kholia/Easy-Digital-Beacons-v1/CW-Beacon-Without-Si5351/Raspberry-Pi-Pico-Pinout.jpg

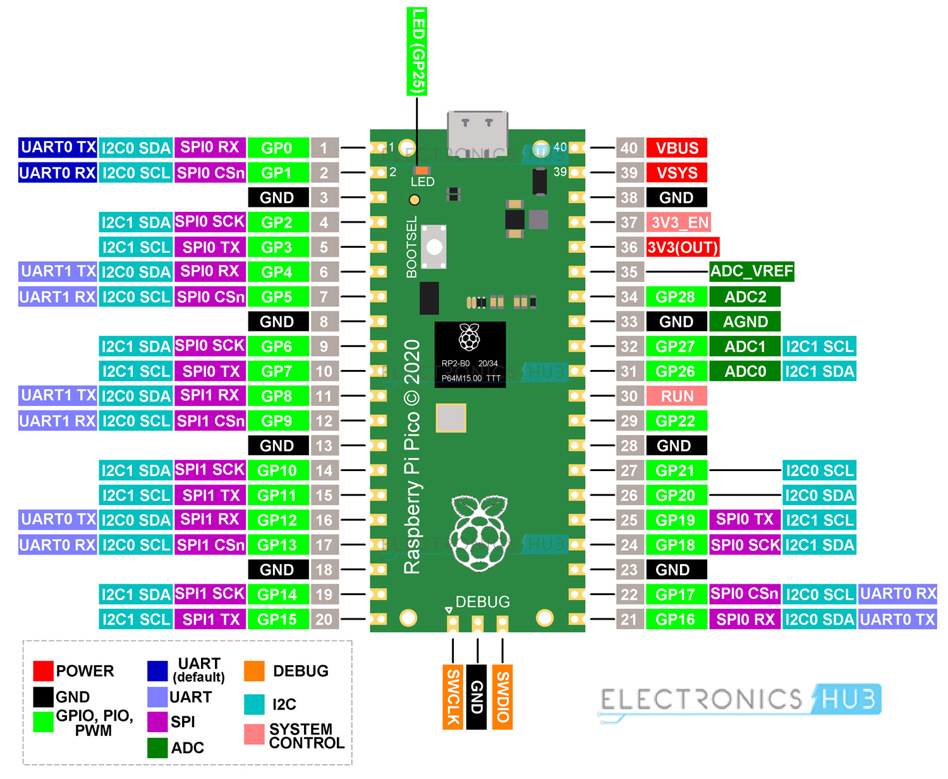
CW-Beacon-Without-Si5351/Raspberry-Pi-Pico-Pinout.jpg
