kholia/Easy-Digital-Beacons-v1/F4GOH-PCB-FST4W-LCD/balise-hf.png

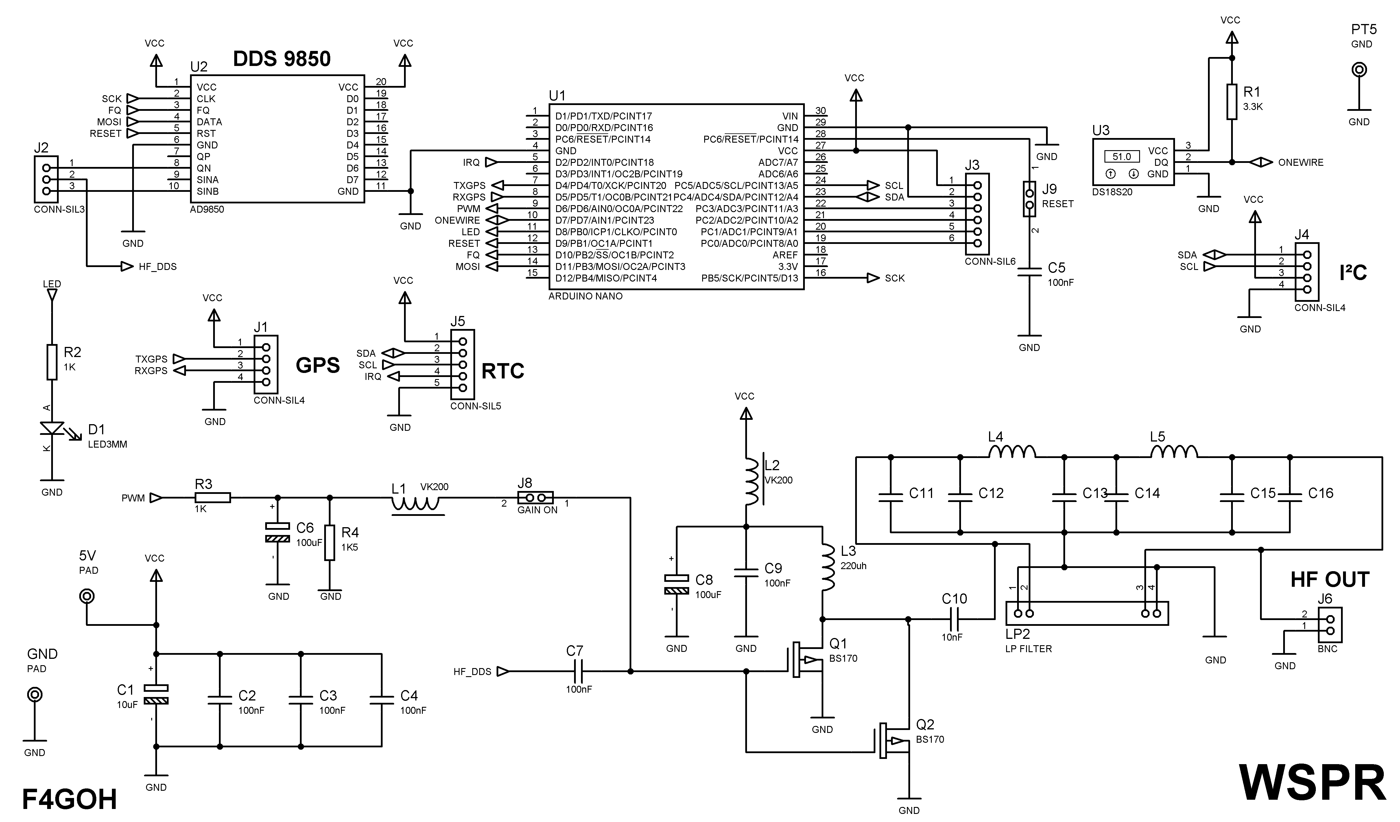
F4GOH-PCB-FST4W-LCD/balise-hf.png
