kholia/Easy-Digital-Beacons-v1/FST4W-GPS-v3-Arduino/Arduino-Nano-Pin-Description-952x1024.jpg

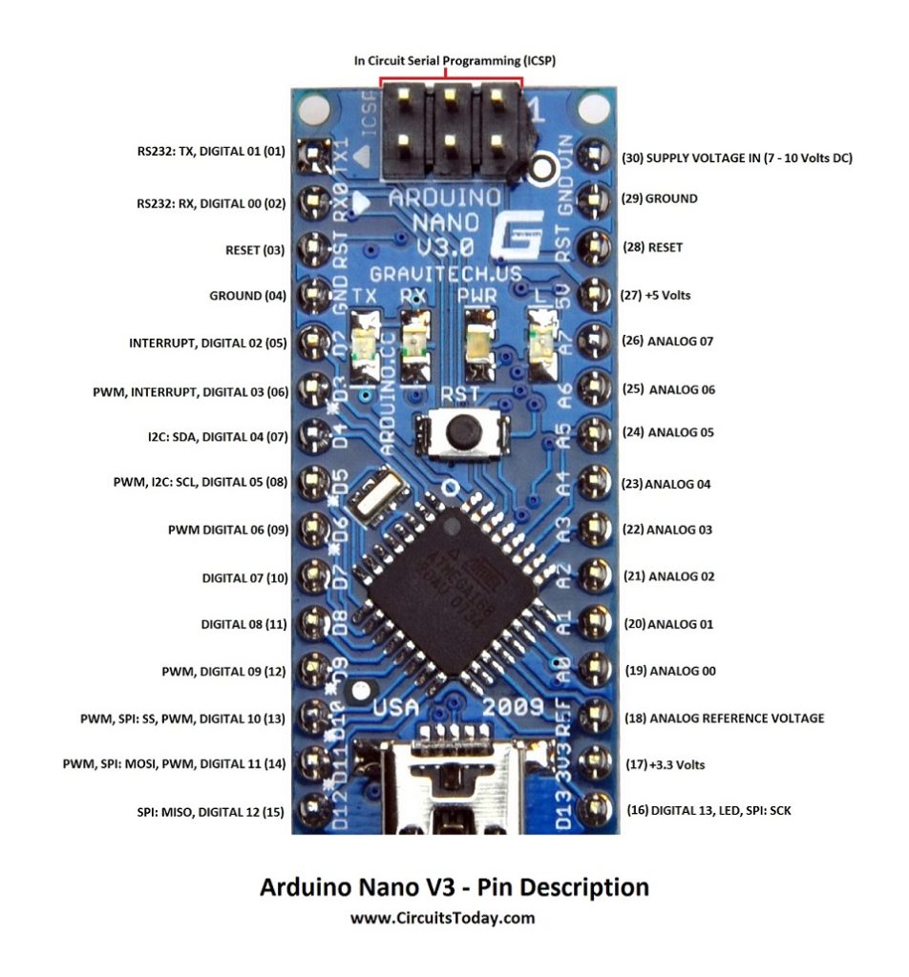
FST4W-GPS-v3-Arduino/Arduino-Nano-Pin-Description-952x1024.jpg
