kholia/Easy-Digital-Beacons-v1/images/MPPico-Base-06-800x800.png

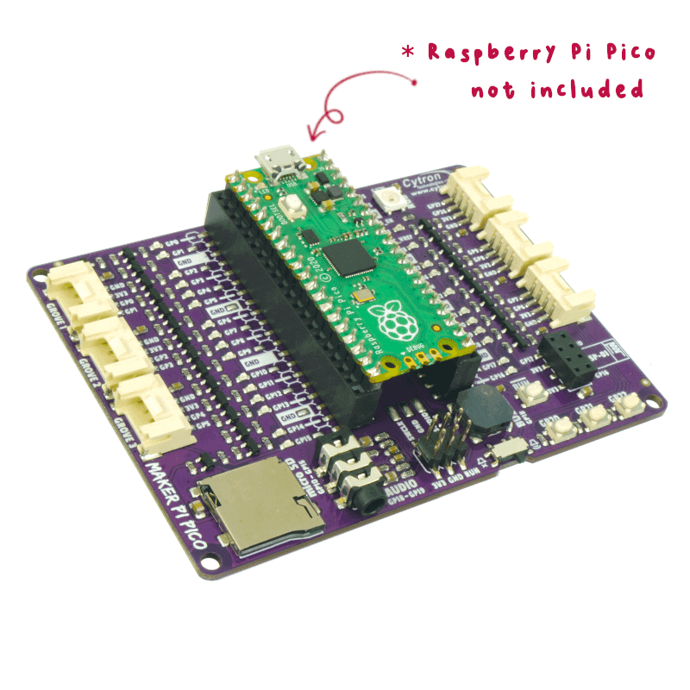
images/MPPico-Base-06-800x800.png
