kholia/Easy-Digital-Beacons-v1/images/Screenshot_2021-10-10_12-11-27.png

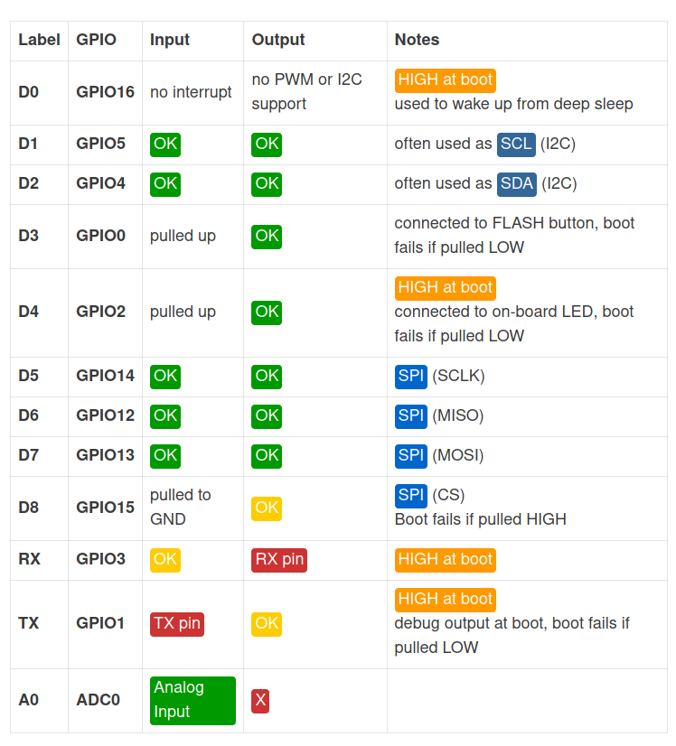
images/Screenshot_2021-10-10_12-11-27.png
