kholia/Easy-Digital-Beacons-v1/Pico-FT8-Beacon-OnlyGPS/Schematic-From-Tony.jpeg

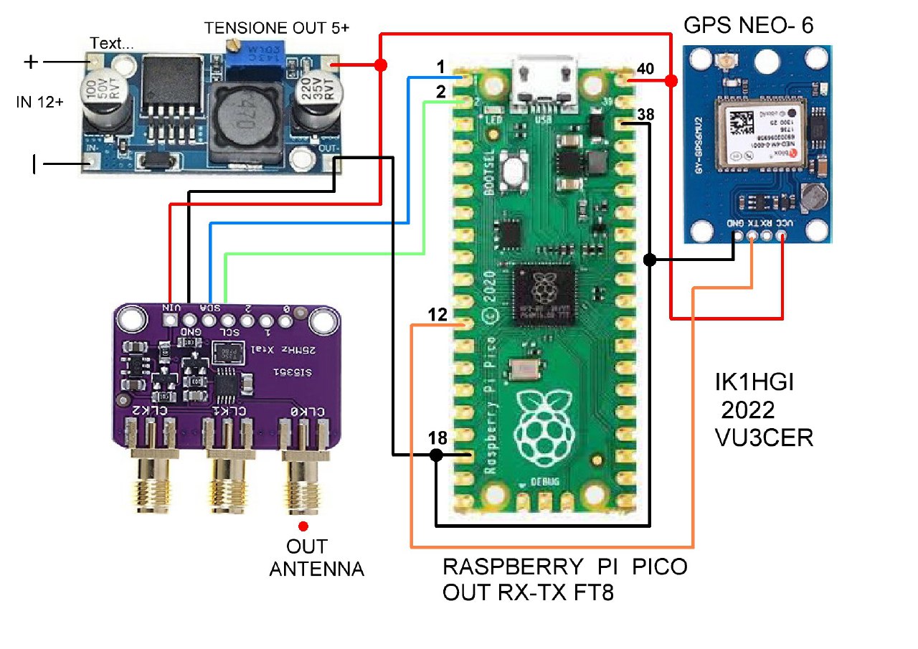
Pico-FT8-Beacon-OnlyGPS/Schematic-From-Tony.jpeg
