kholia/Easy-Digital-Beacons-v1/Pixie-WSPR-ESP8266/pixie+modified.jpg

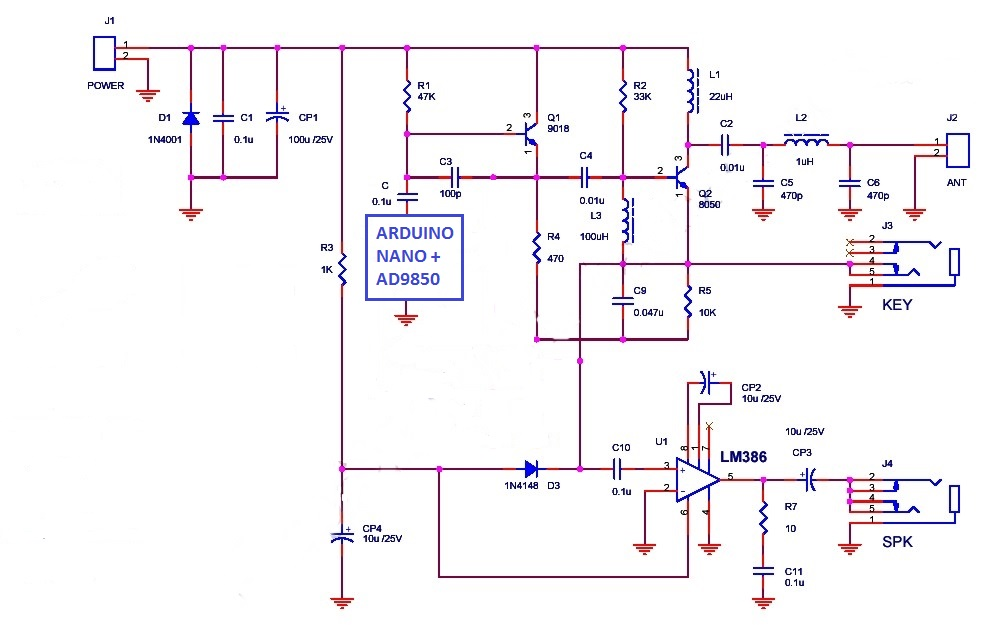
Pixie-WSPR-ESP8266/pixie+modified.jpg
