kholia/Easy-Digital-Beacons-v1/Pixie-WSPR-ESP8266/pixie+schematic.jpg

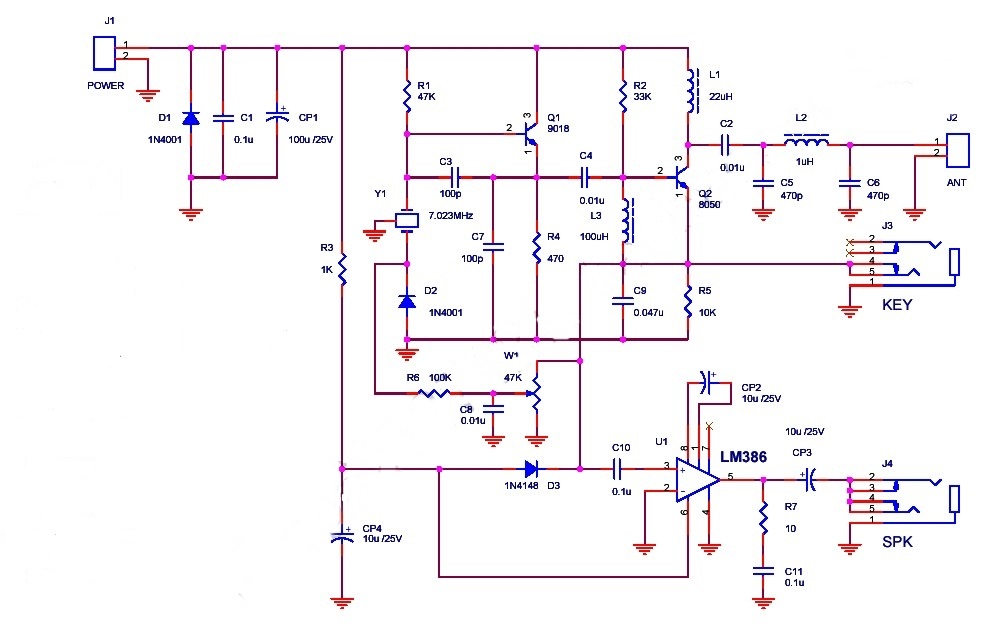
Pixie-WSPR-ESP8266/pixie+schematic.jpg
