kholia/Easy-Digital-Beacons-v1/Pixie-WSPR-ESP8266/Pixie-WSPR-Hack.jpg

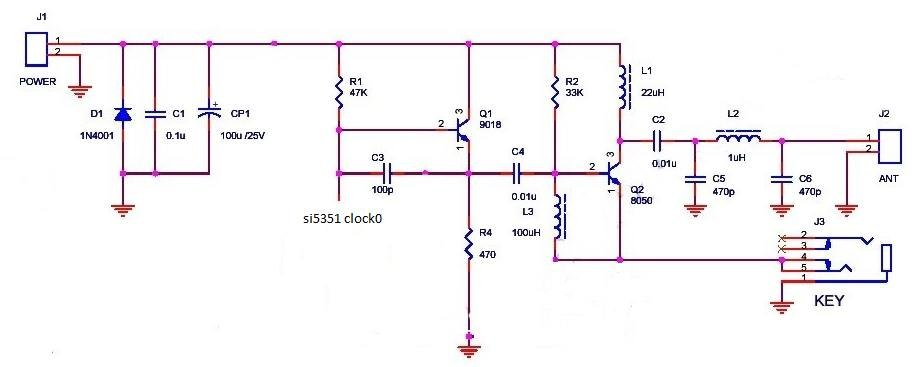
Pixie-WSPR-ESP8266/Pixie-WSPR-Hack.jpg
