kholia/Easy-Digital-Beacons-v1/Pixie-WSPR-ESP8266/Real-Life-Picture-2.jpg

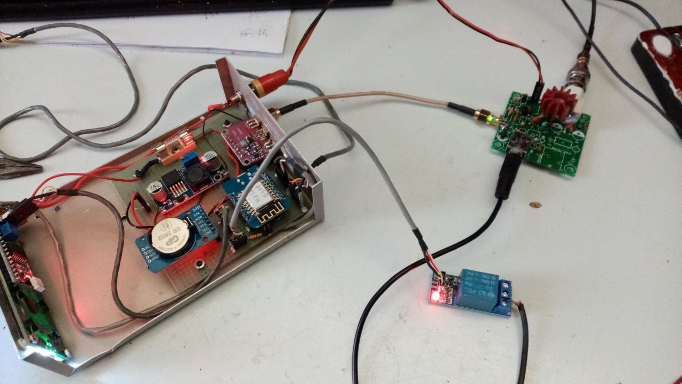
Pixie-WSPR-ESP8266/Real-Life-Picture-2.jpg
