kholia/Easy-Digital-Beacons-v1/Pixie-WSPR-ESP8266/Real-Life-Picture.jpg

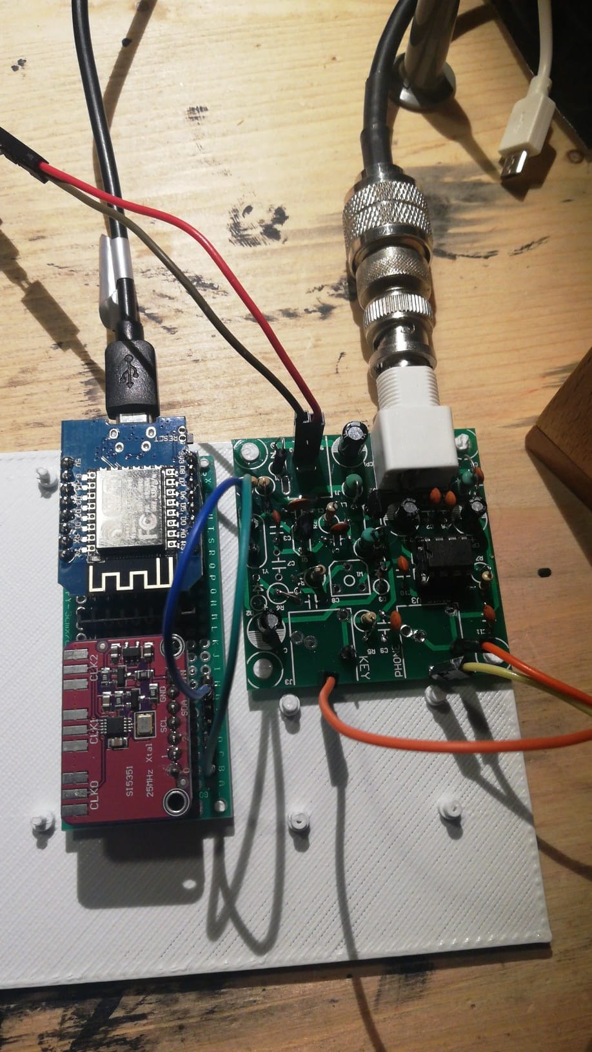
Pixie-WSPR-ESP8266/Real-Life-Picture.jpg
