kholia/Easy-Digital-Beacons-v1/screenshots/1 Channel Relay Module (Active Low Control).jpg

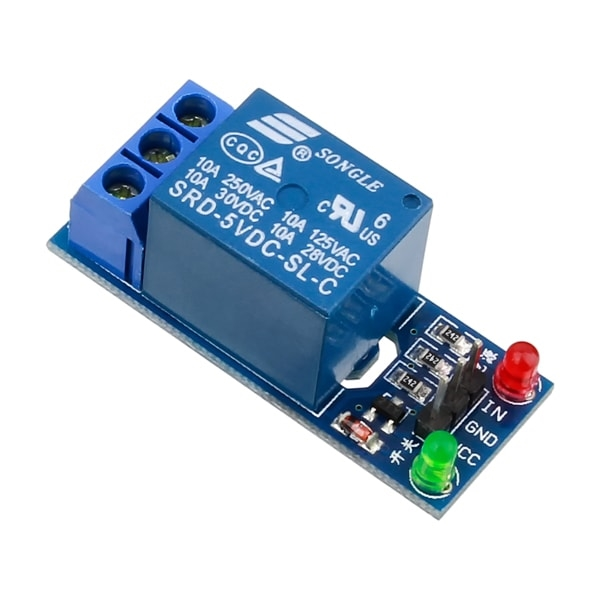
screenshots/1 Channel Relay Module (Active Low Control).jpg
