kholia/Easy-Digital-Beacons-v1/screenshots/120TR-Screenshot_2022-03-21_17-04-42.png

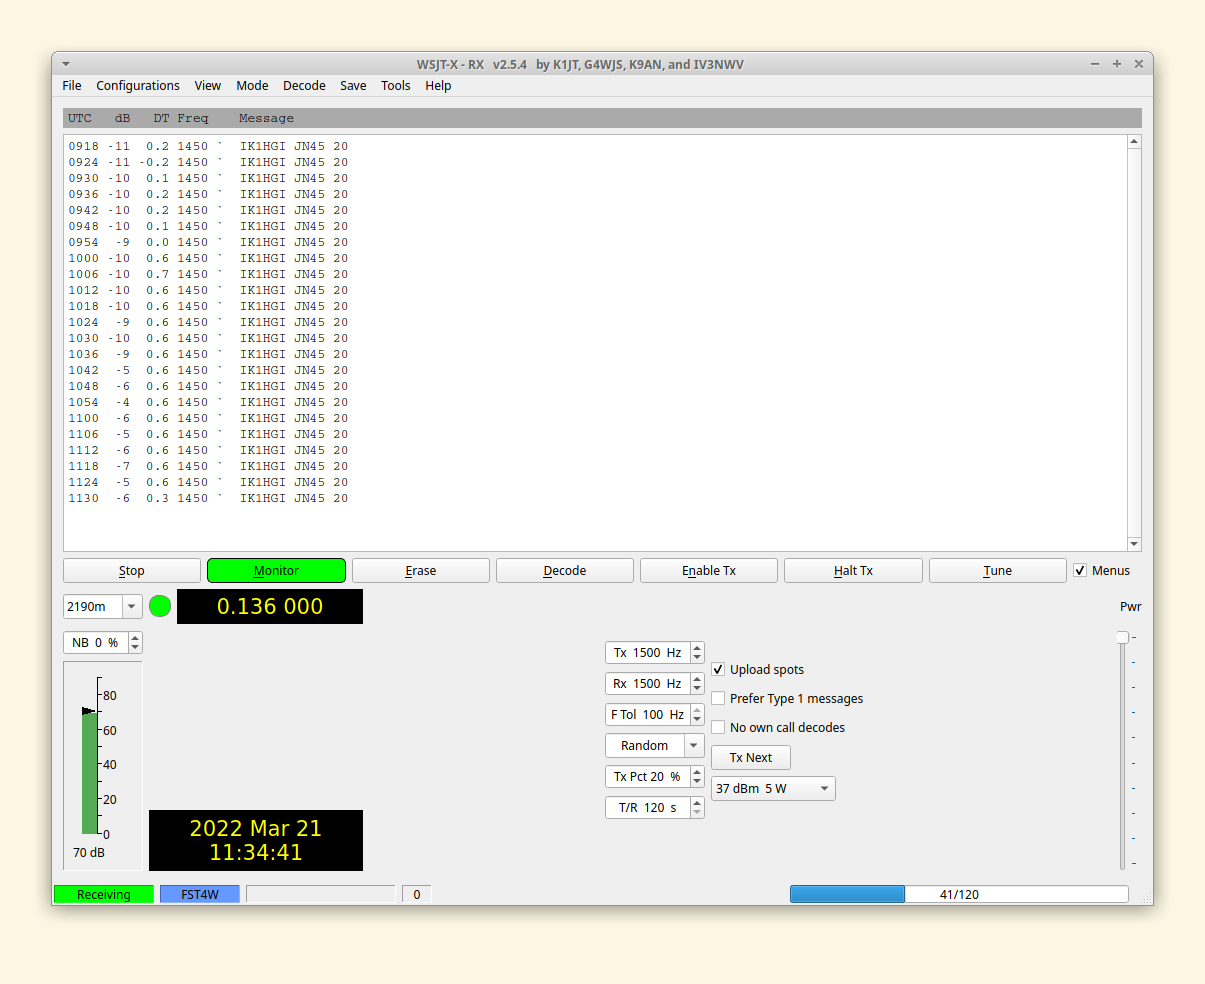
screenshots/120TR-Screenshot_2022-03-21_17-04-42.png
