kholia/Easy-Digital-Beacons-v1/screenshots/300TR-Multiple-Success-Screenshot_2022-03-21_18-41-07.png

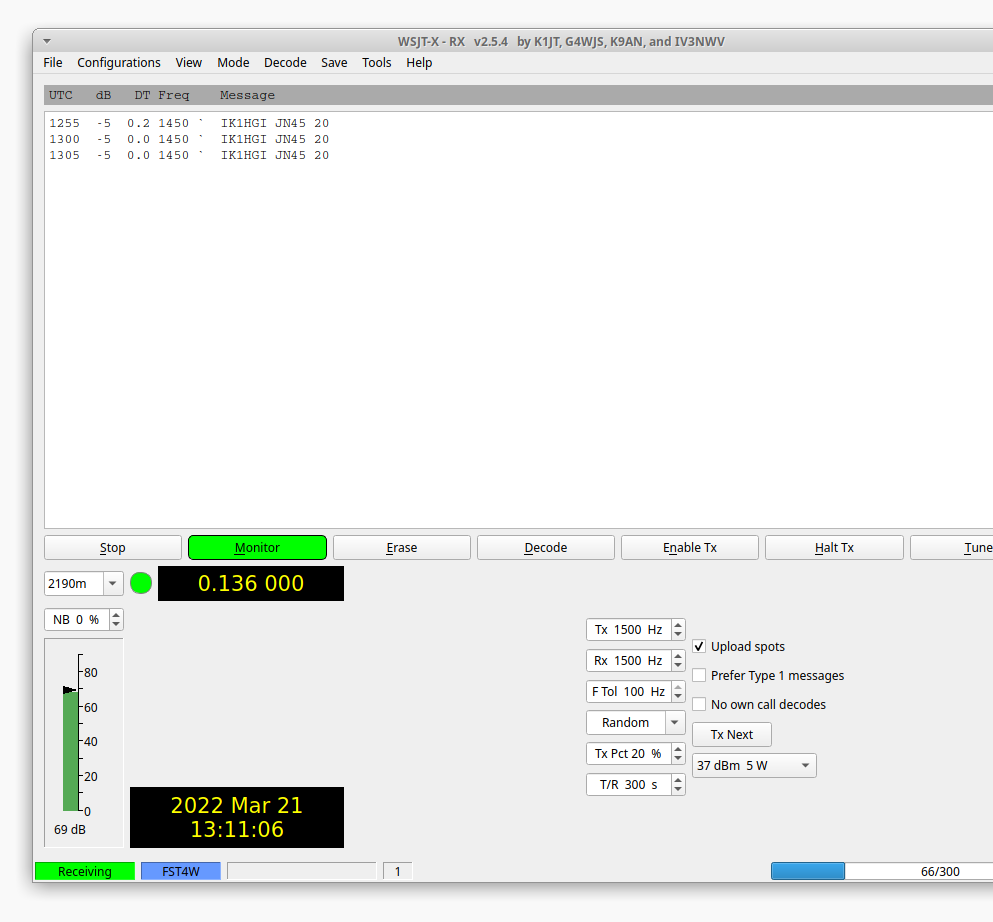
screenshots/300TR-Multiple-Success-Screenshot_2022-03-21_18-41-07.png
