kholia/Easy-Digital-Beacons-v1/screenshots/300TR-Screenshot_2022-03-21_18-15-22.png

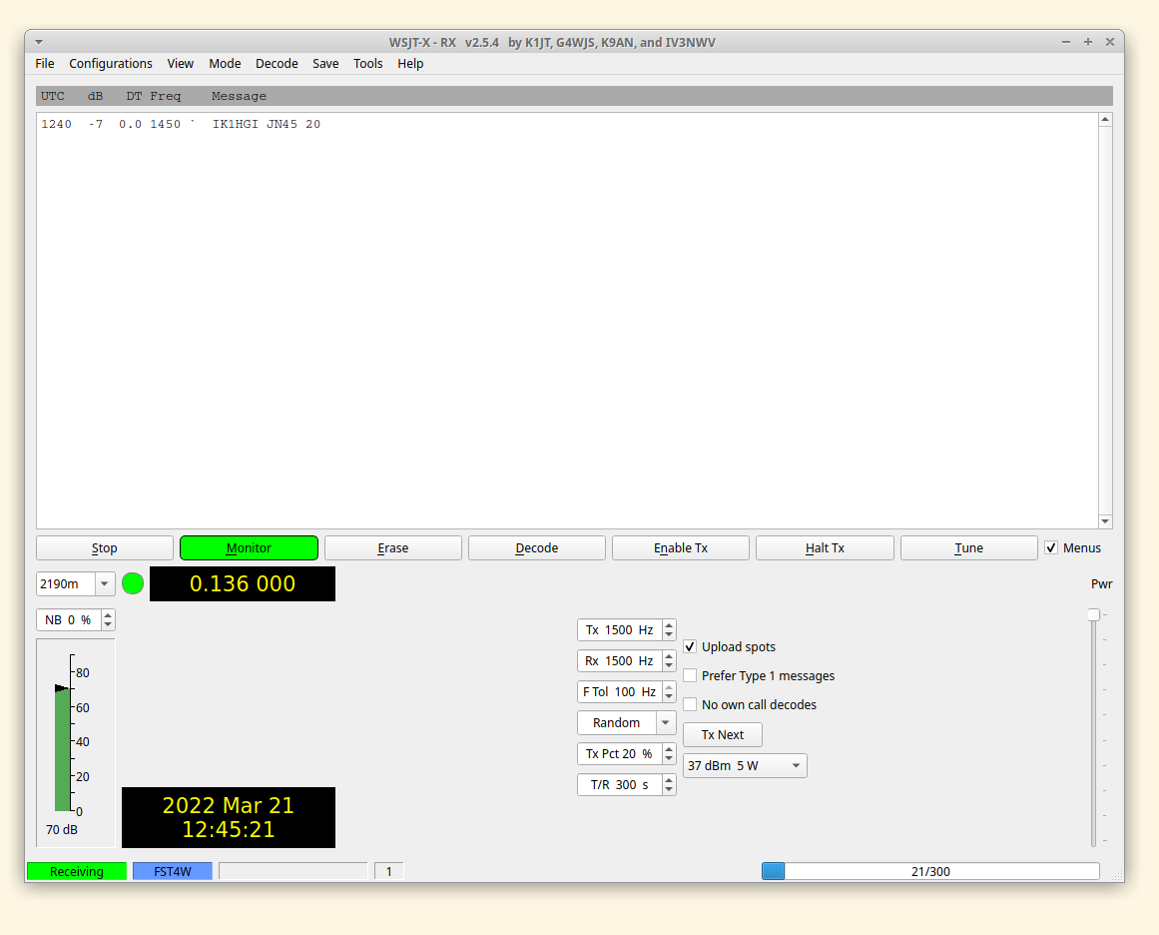
screenshots/300TR-Screenshot_2022-03-21_18-15-22.png
