kholia/Easy-Digital-Beacons-v1/screenshots/900TR-Screenshot_2022-03-21_19-31-47.png

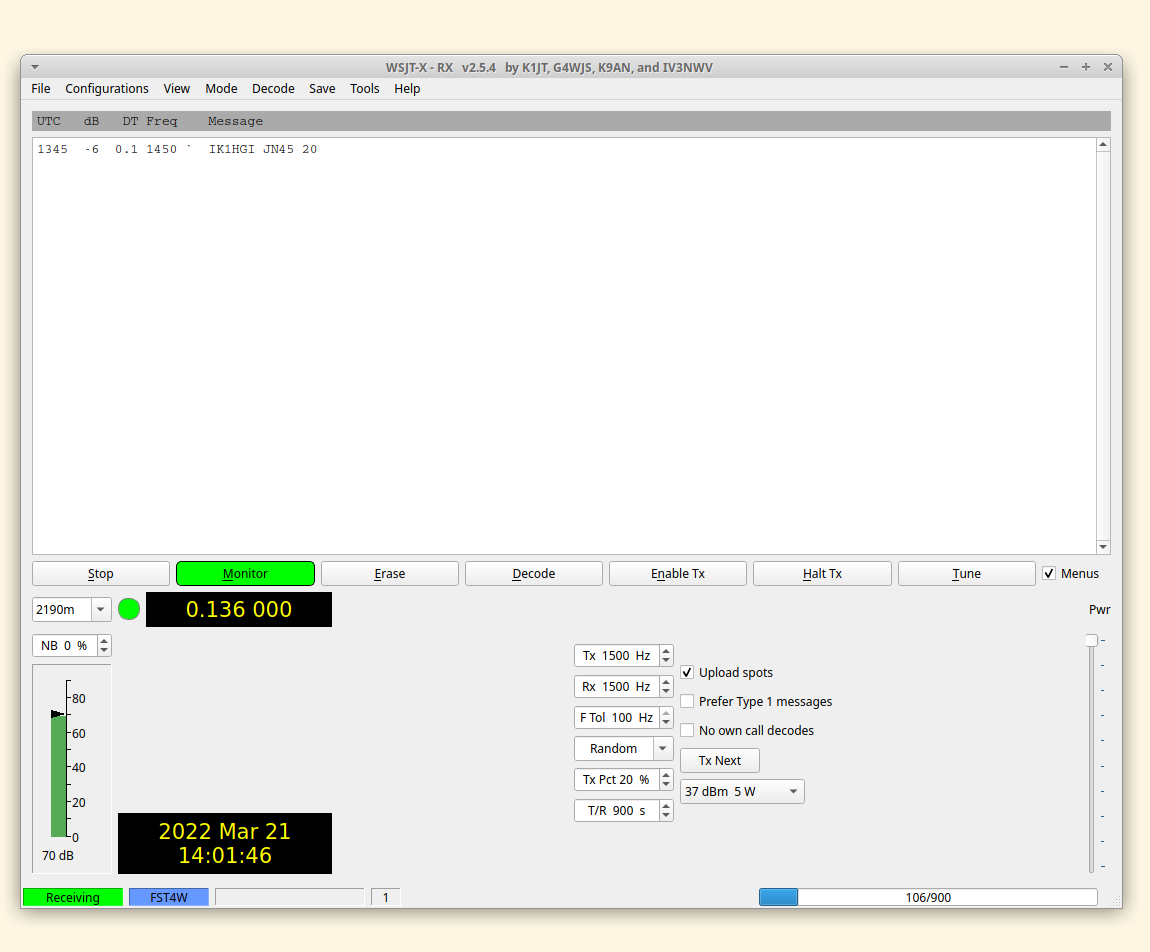
screenshots/900TR-Screenshot_2022-03-21_19-31-47.png
