kholia/Easy-Digital-Beacons-v1/screenshots/From-Arduino-w00t-Screenshot_2022-04-02_21-06-24.png

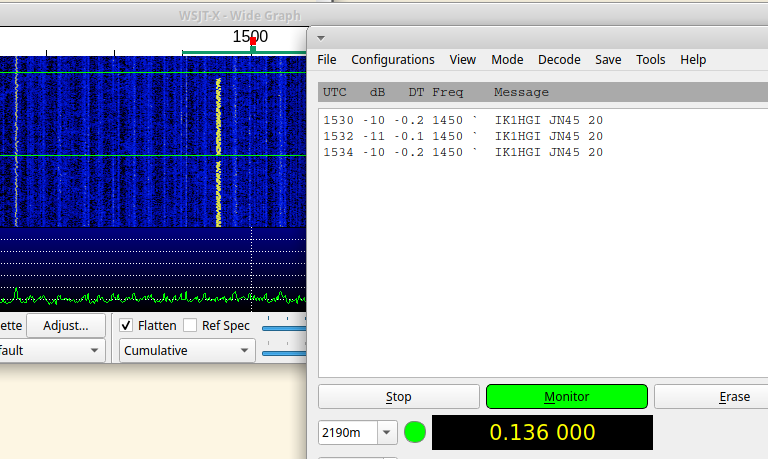
screenshots/From-Arduino-w00t-Screenshot_2022-04-02_21-06-24.png
