kholia/Easy-Digital-Beacons-v1/screenshots/FST4W-Waterfall-Screenshot_2022-04-02_20-24-25.png

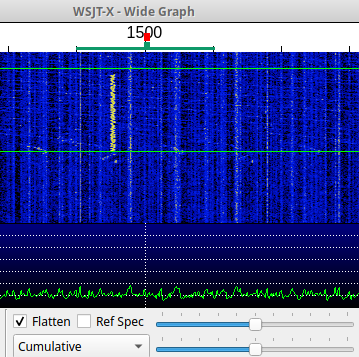
screenshots/FST4W-Waterfall-Screenshot_2022-04-02_20-24-25.png
