kholia/Easy-Digital-Beacons-v1/screenshots/FT4-First-Decodes-10-Oct-2021.png

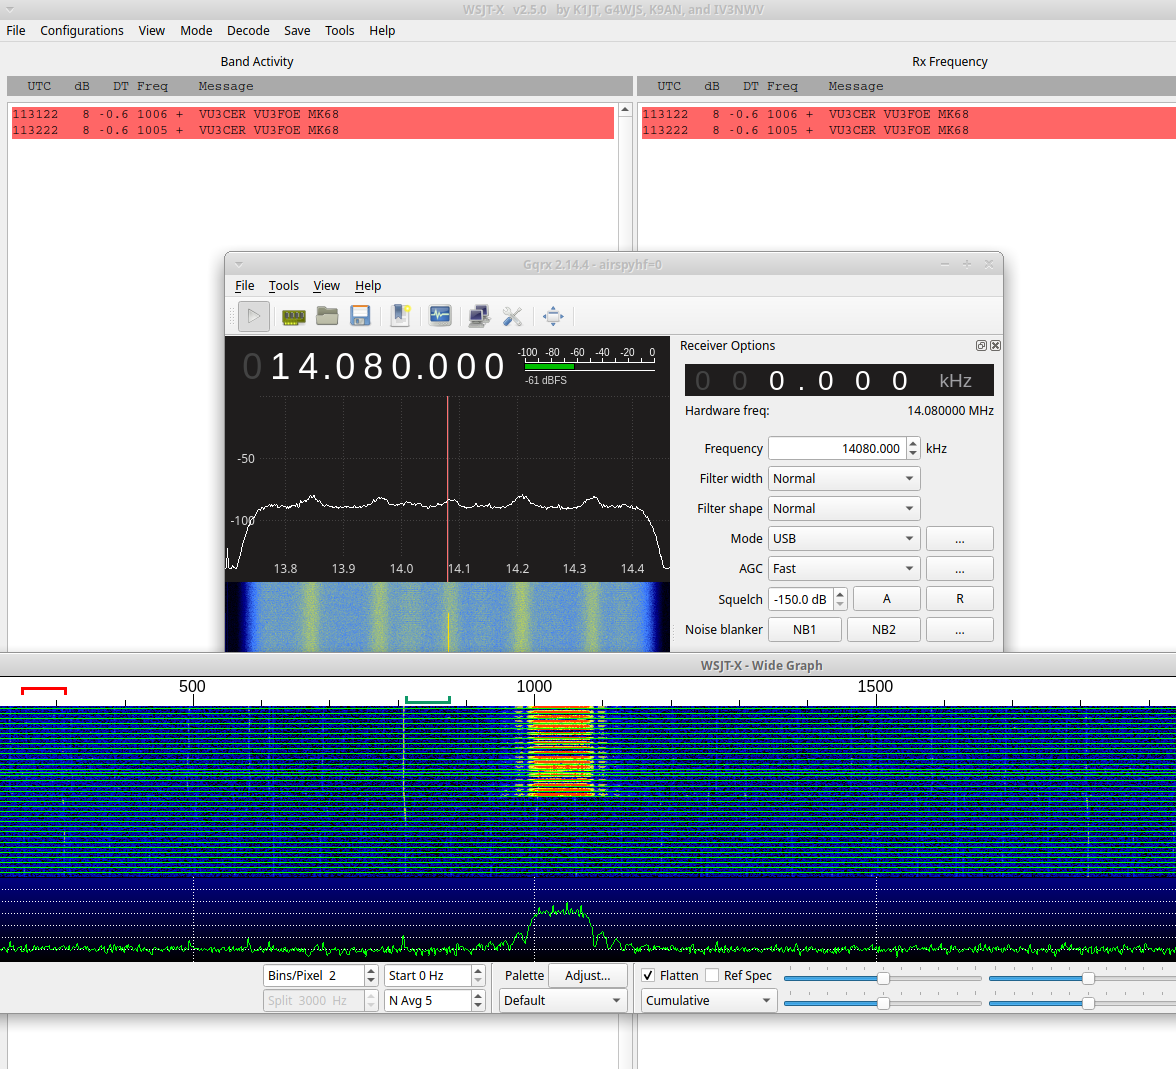
screenshots/FT4-First-Decodes-10-Oct-2021.png
