kholia/Easy-Digital-Beacons-v1/screenshots/Screenshot_2021-07-17_17-29-49.png

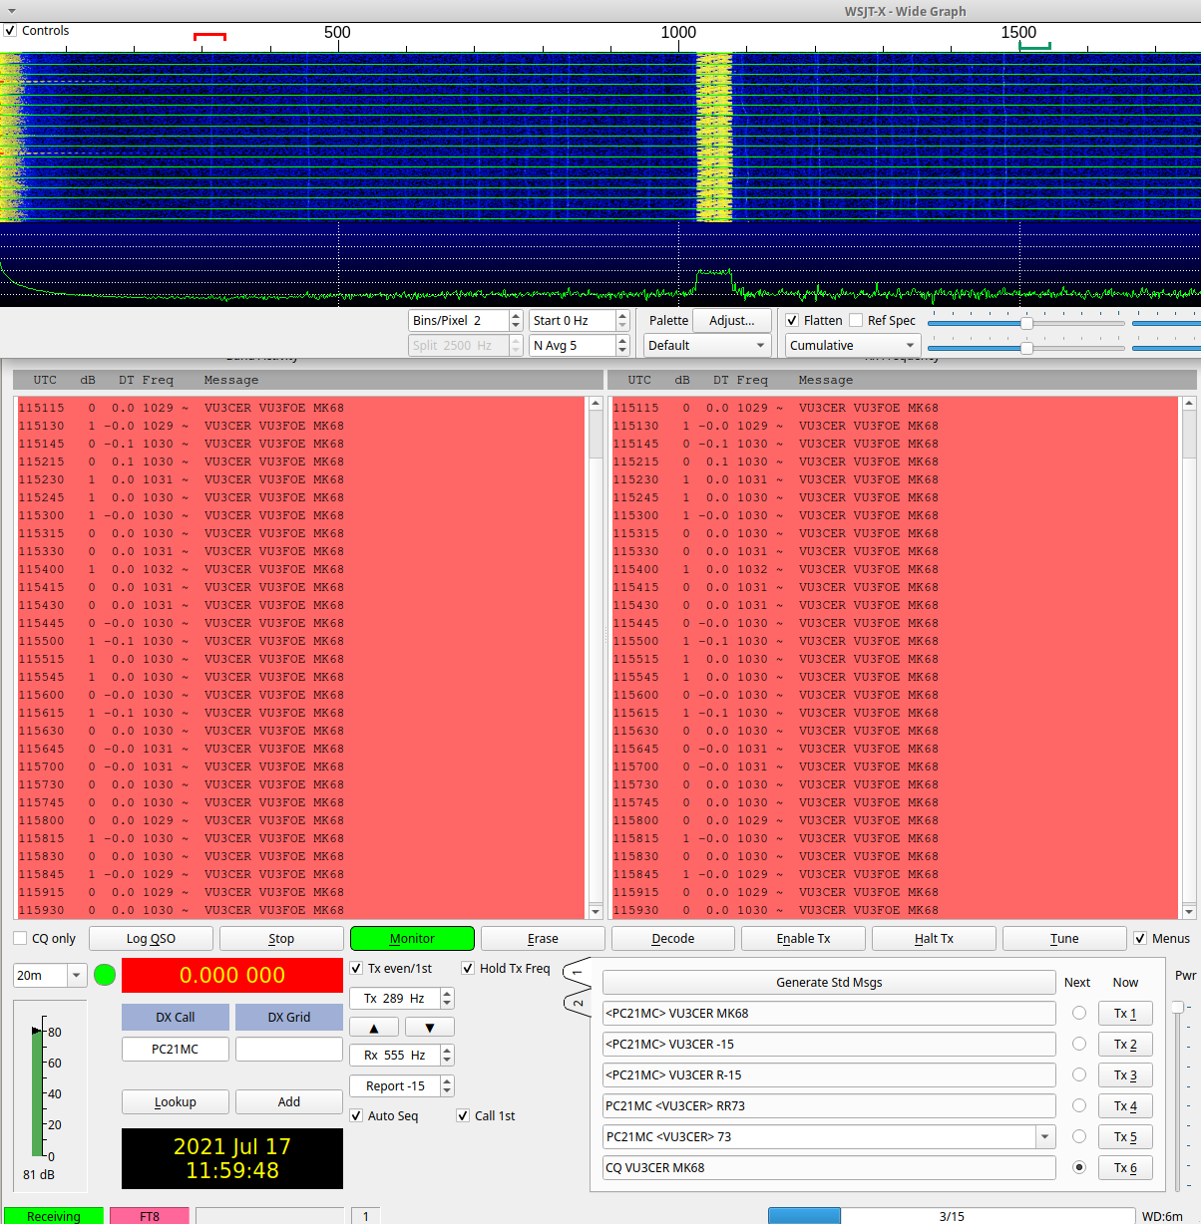
screenshots/Screenshot_2021-07-17_17-29-49.png
