kholia/Easy-Digital-Beacons-v1/screenshots/Screenshot_2021-10-10_17-06-39.png

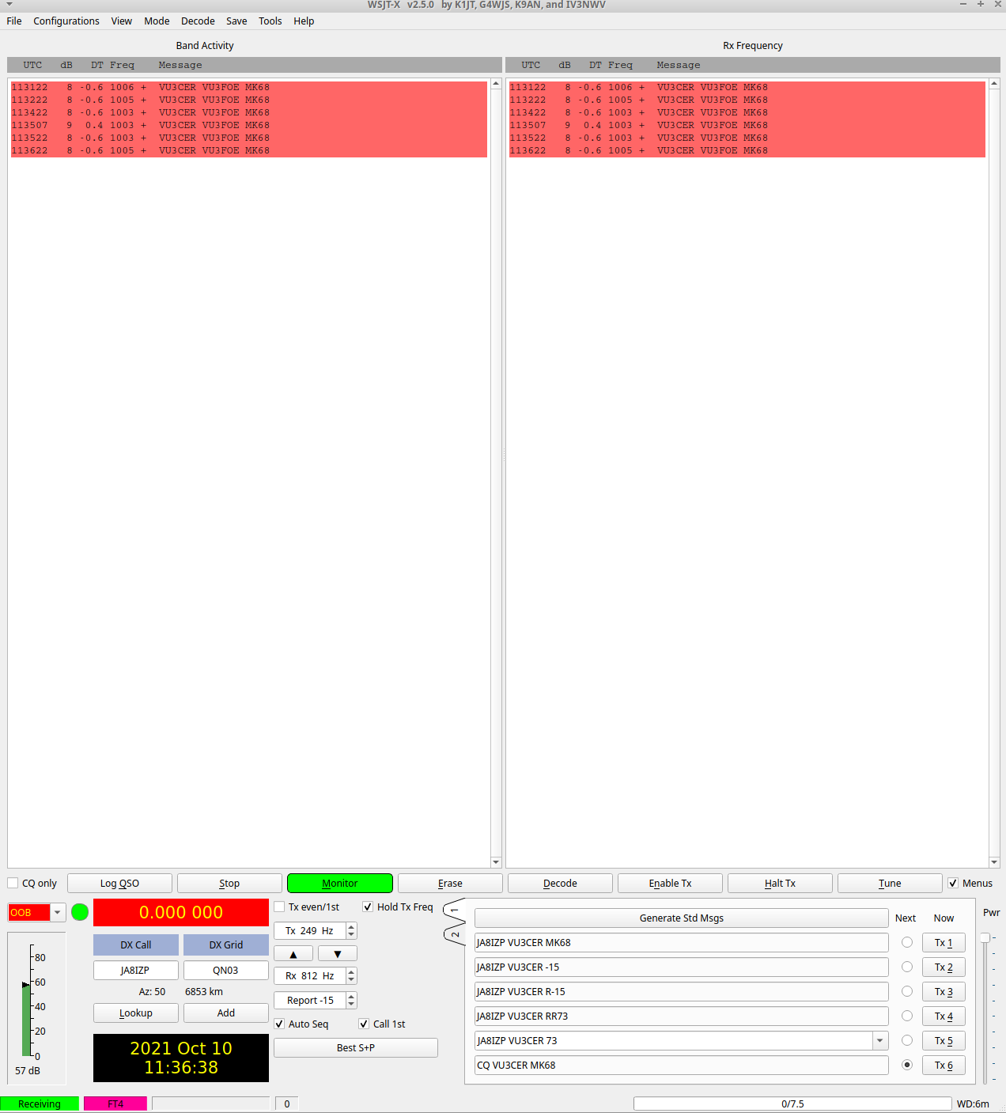
screenshots/Screenshot_2021-10-10_17-06-39.png
