kholia/Easy-Digital-Beacons-v1/screenshots/Screenshot_2022-03-17_16-31-43.png

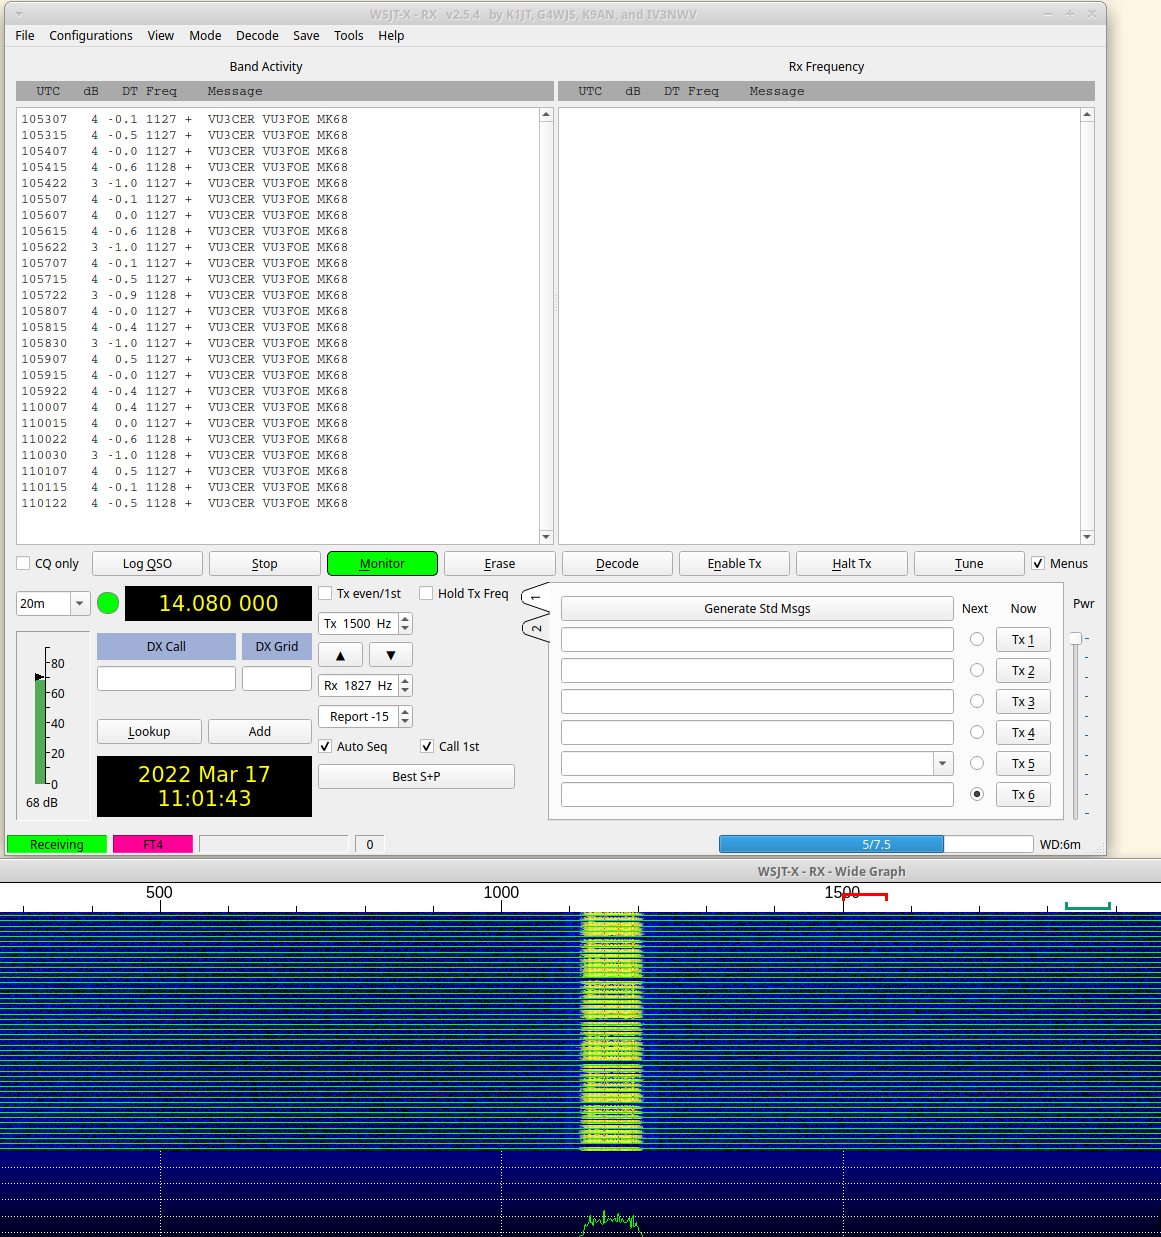
screenshots/Screenshot_2022-03-17_16-31-43.png
