kholia/Easy-Digital-Beacons-v1/screenshots/Screenshot_2022-03-19_17-35-52.png

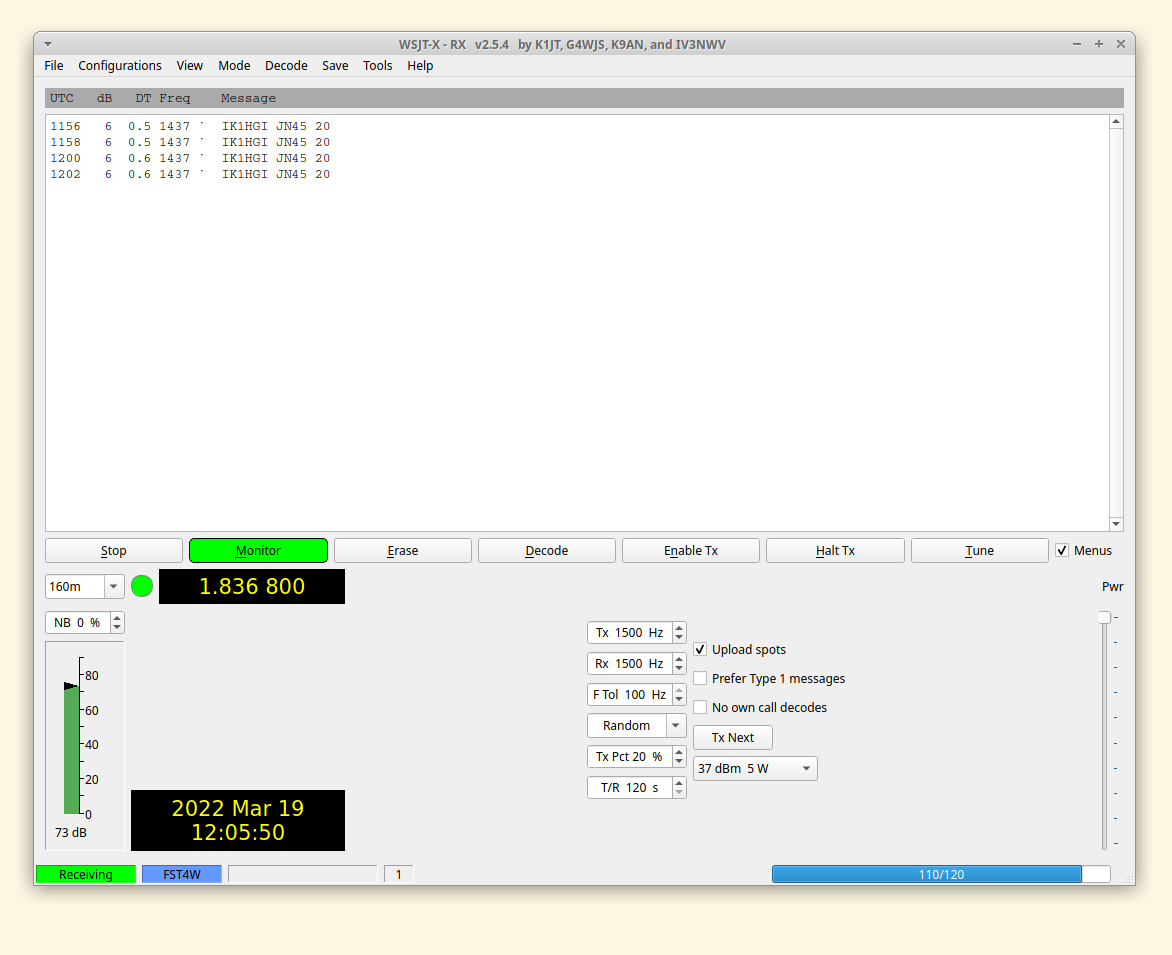
screenshots/Screenshot_2022-03-19_17-35-52.png
