kholia/Easy-Digital-Beacons-v1/screenshots/Screenshot_2022-03-19_17-44-00.png

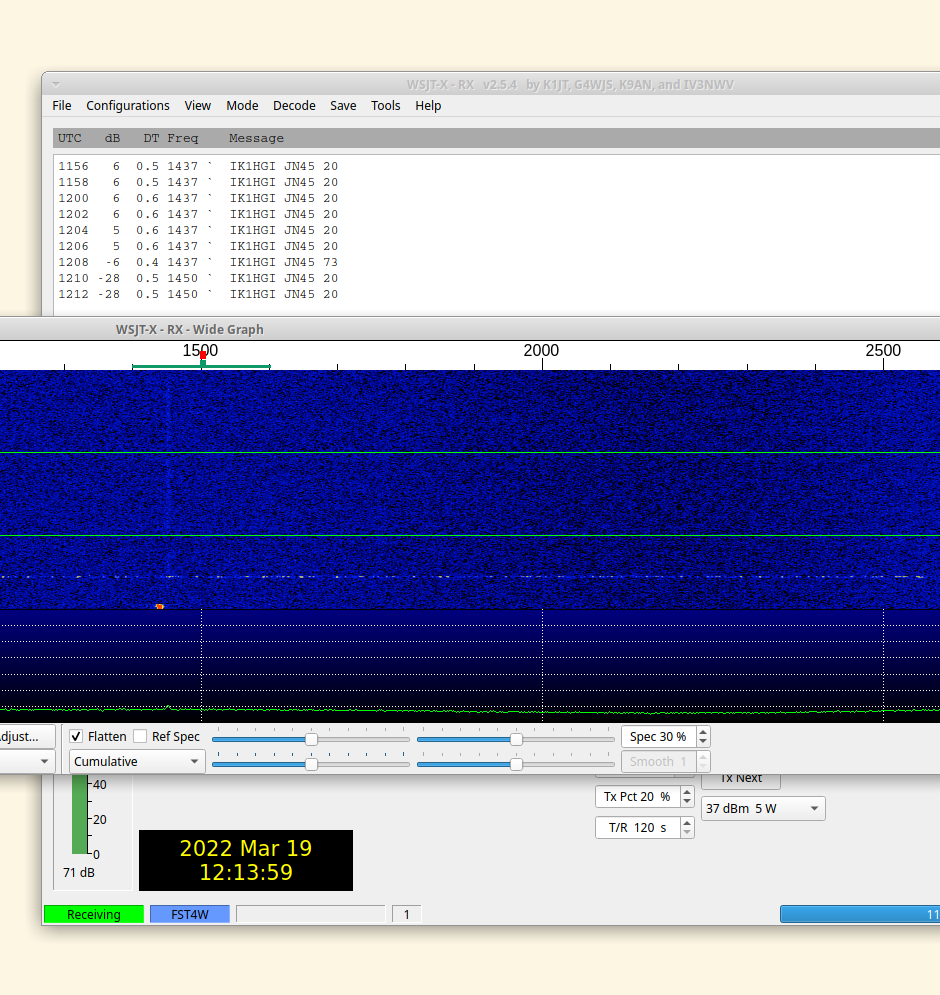
screenshots/Screenshot_2022-03-19_17-44-00.png
