kholia/Easy-Digital-Beacons-v1/screenshots/Screenshot_2022-03-19_23-04-40.png

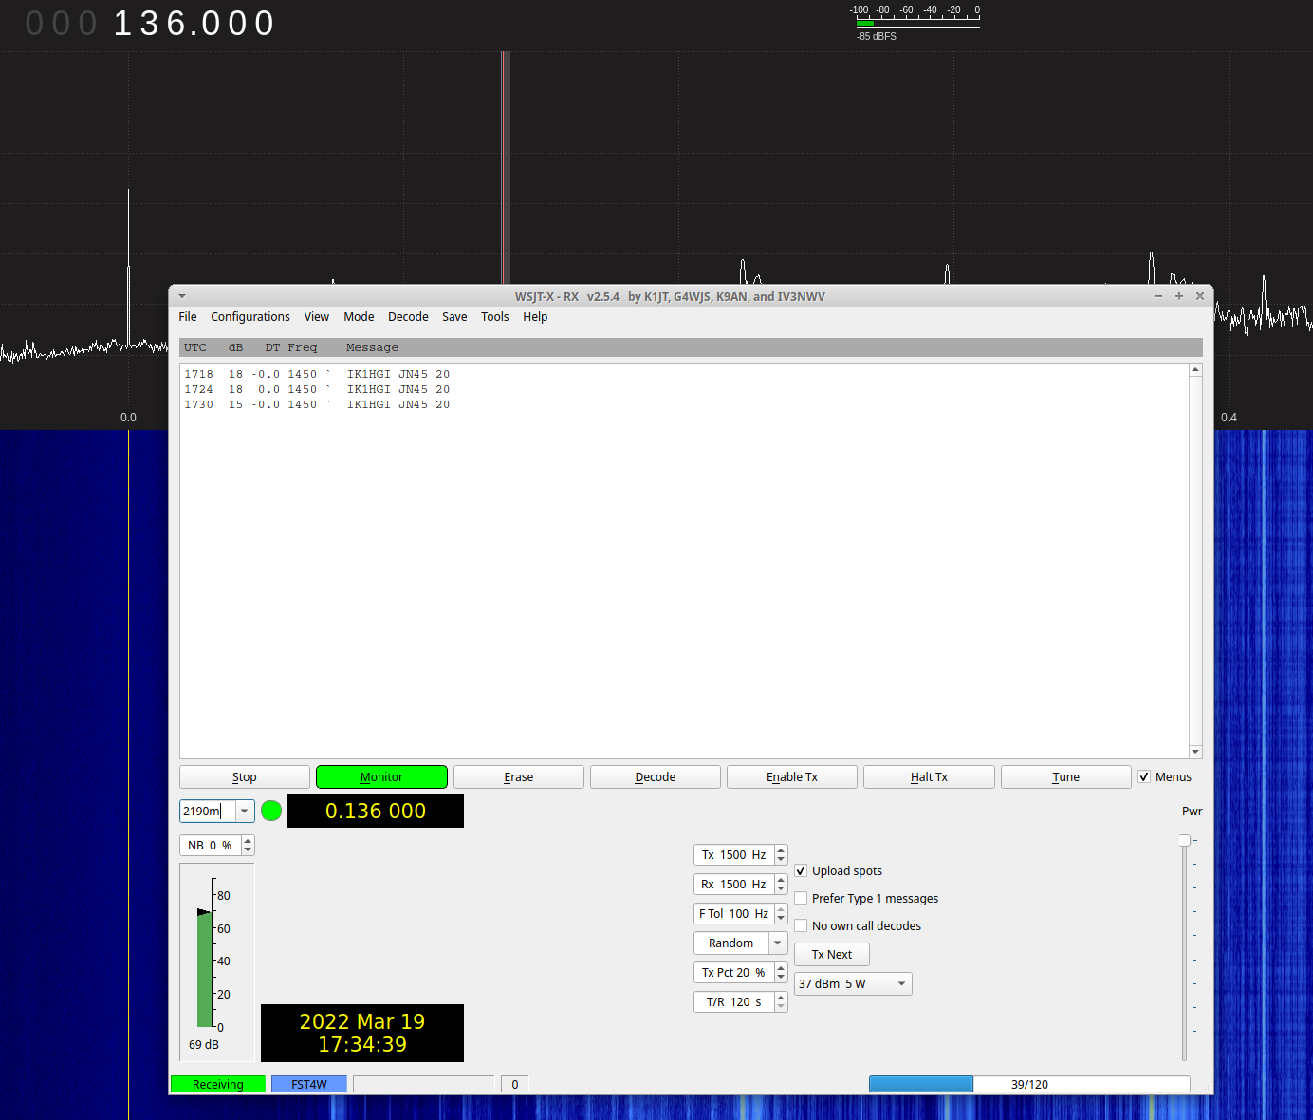
screenshots/Screenshot_2022-03-19_23-04-40.png
