kholia/Easy-Digital-Beacons-v1/screenshots/Screenshot_2022-03-21_14-44-34.png

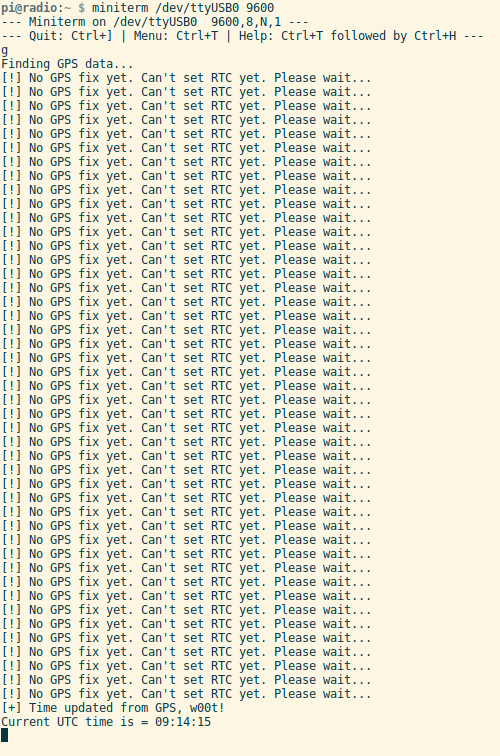
screenshots/Screenshot_2022-03-21_14-44-34.png
