kholia/Easy-Digital-Beacons-v1/Top-Band-LPF/Screenshot_2022-03-20_19-14-18.png

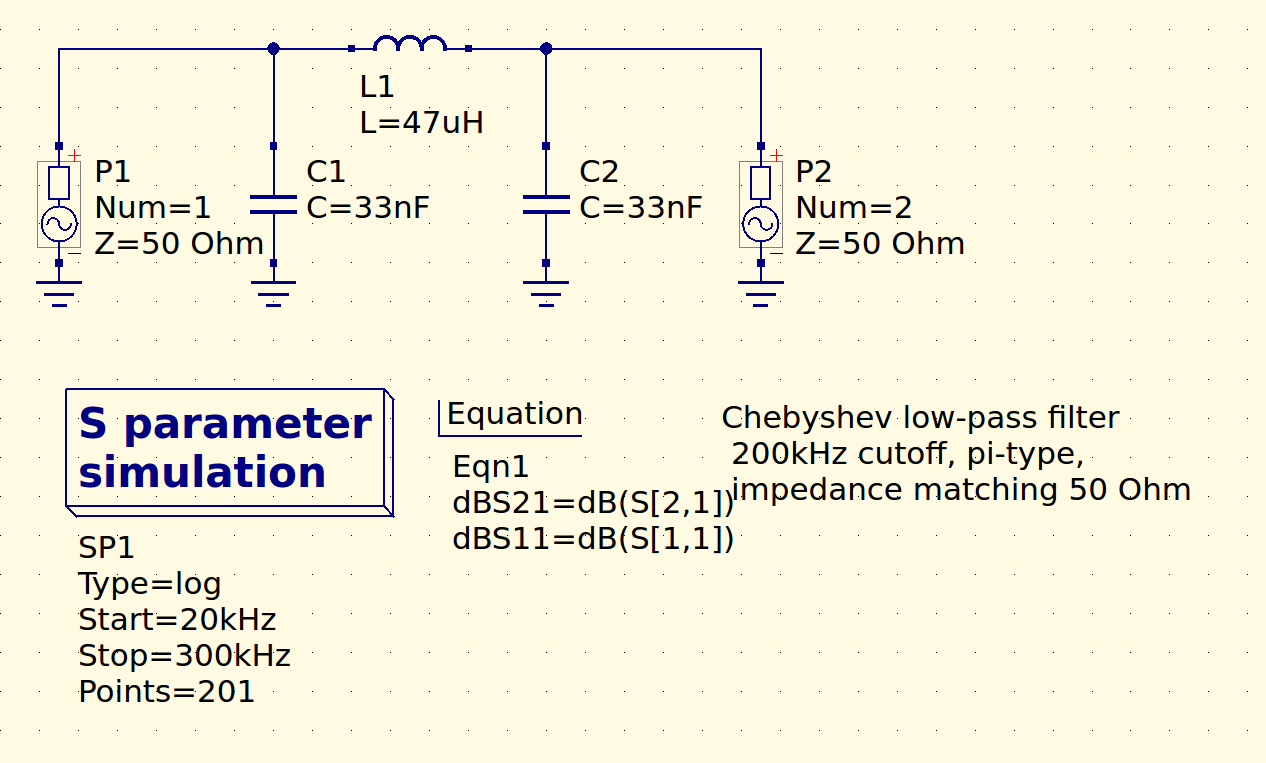
Top-Band-LPF/Screenshot_2022-03-20_19-14-18.png
