kholia/Easy-Digital-Beacons-v1/Si5351_Calibration_Pico/I2C On Pico.png

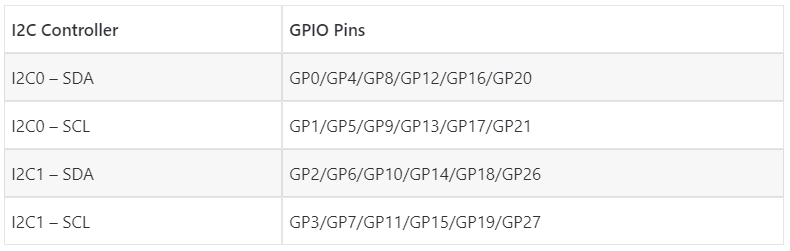
Si5351_Calibration_Pico/I2C On Pico.png
