kholia/Easy-Digital-Beacons-v1/Easy-Digital-Beacons-v4/MyFont.h

#include <Arduino.h>
// Created by http://oleddisplay.squix.ch/ Consider a donation
// In case of problems make sure that you are using the font file with the correct version!
const uint8_t Roboto_Mono_Thin_16[] PROGMEM = {
	0x0A, // Width: 10
	0x13, // Height: 19
	0x20, // First Char: 32
	0xE0, // Numbers of Chars: 224

	// Jump Table:
	0xFF, 0xFF, 0x00, 0x0A, // 32:65535
	0x00, 0x00, 0x0E, 0x0A, // 33:0
	0x00, 0x0E, 0x10, 0x0A, // 34:14
	0x00, 0x1E, 0x1A, 0x0A, // 35:30
	0x00, 0x38, 0x17, 0x0A, // 36:56
	0x00, 0x4F, 0x1A, 0x0A, // 37:79
	0x00, 0x69, 0x1A, 0x0A, // 38:105
	0x00, 0x83, 0x0D, 0x0A, // 39:131
	0x00, 0x90, 0x15, 0x0A, // 40:144
	0x00, 0xA5, 0x11, 0x0A, // 41:165
	0x00, 0xB6, 0x17, 0x0A, // 42:182
	0x00, 0xCD, 0x1A, 0x0A, // 43:205
	0x00, 0xE7, 0x0C, 0x0A, // 44:231
	0x00, 0xF3, 0x14, 0x0A, // 45:243
	0x01, 0x07, 0x11, 0x0A, // 46:263
	0x01, 0x18, 0x16, 0x0A, // 47:280
	0x01, 0x2E, 0x17, 0x0A, // 48:302
	0x01, 0x45, 0x11, 0x0A, // 49:325
	0x01, 0x56, 0x17, 0x0A, // 50:342
	0x01, 0x6D, 0x17, 0x0A, // 51:365
	0x01, 0x84, 0x1A, 0x0A, // 52:388
	0x01, 0x9E, 0x17, 0x0A, // 53:414
	0x01, 0xB5, 0x17, 0x0A, // 54:437
	0x01, 0xCC, 0x16, 0x0A, // 55:460
	0x01, 0xE2, 0x1A, 0x0A, // 56:482
	0x01, 0xFC, 0x17, 0x0A, // 57:508
	0x02, 0x13, 0x11, 0x0A, // 58:531
	0x02, 0x24, 0x11, 0x0A, // 59:548
	0x02, 0x35, 0x17, 0x0A, // 60:565
	0x02, 0x4C, 0x17, 0x0A, // 61:588
	0x02, 0x63, 0x17, 0x0A, // 62:611
	0x02, 0x7A, 0x16, 0x0A, // 63:634
	0x02, 0x90, 0x1A, 0x0A, // 64:656
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
	0x00, 0x00, 0x00, 0xE0, 0x1F, 0x00, 0x10, 0x20, 0x00, 0x08, 0x40, 0x00, 0x08, 0x40, 0x00, 0x08, 0x42, 0x00, 0x08, 0x42, 0x00, 0x30, 0x3E,									  // 71
	0x00, 0x00, 0x00, 0xF8, 0x7F, 0x00, 0x00, 0x01, 0x00, 0x00, 0x01, 0x00, 0x00, 0x01, 0x00, 0x00, 0x01, 0x00, 0x00, 0x01, 0x00, 0xF8, 0x7F,									  // 72
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
};
