kholia/Easy-Digital-Beacons-v1/Easy-Digital-Beacons-v4/constants.cpp

#include "constants.h"

// Costas sync tone pattern
const uint8_t kFT8_Costas_pattern[7] = {3, 1, 4, 0, 6, 5, 2};
const uint8_t kFT4_Costas_pattern[4][4] = {
    {0, 1, 3, 2},
    {1, 0, 2, 3},
    {2, 3, 1, 0},
    {3, 2, 0, 1}};

// Gray code map (FTx bits -> channel symbols)
const uint8_t kFT8_Gray_map[8] = {0, 1, 3, 2, 5, 6, 4, 7};
const uint8_t kFT4_Gray_map[4] = {0, 1, 3, 2};

const uint8_t kFT4_XOR_sequence[10] = {
    0x4Au, // 01001010
    0x5Eu, // 01011110
    0x89u, // 10001001
    0xB4u, // 10110100
    0xB0u, // 10110000
    0x8Au, // 10001010
    0x79u, // 01111001
    0x55u, // 01010101
    0xBEu, // 10111110
    0x28u, // 00101 [000]
};

// Parity generator matrix for (174,91) LDPC code, stored in bitpacked format (MSB first)
const uint8_t kFTX_LDPC_generator[FTX_LDPC_M][FTX_LDPC_K_BYTES] = {
    {0x83, 0x29, 0xce, 0x11, 0xbf, 0x31, 0xea, 0xf5, 0x09, 0xf2, 0x7f, 0xc0},
    {0x76, 0x1c, 0x26, 0x4e, 0x25, 0xc2, 0x59, 0x33, 0x54, 0x93, 0x13, 0x20},
    {0xdc, 0x26, 0x59, 0x02, 0xfb, 0x27, 0x7c, 0x64, 0x10, 0xa1, 0xbd, 0xc0},
    {0x1b, 0x3f, 0x41, 0x78, 0x58, 0xcd, 0x2d, 0xd3, 0x3e, 0xc7, 0xf6, 0x20},
    {0x09, 0xfd, 0xa4, 0xfe, 0xe0, 0x41, 0x95, 0xfd, 0x03, 0x47, 0x83, 0xa0},
    {0x07, 0x7c, 0xcc, 0xc1, 0x1b, 0x88, 0x73, 0xed, 0x5c, 0x3d, 0x48, 0xa0},
    {0x29, 0xb6, 0x2a, 0xfe, 0x3c, 0xa0, 0x36, 0xf4, 0xfe, 0x1a, 0x9d, 0xa0},
    {0x60, 0x54, 0xfa, 0xf5, 0xf3, 0x5d, 0x96, 0xd3, 0xb0, 0xc8, 0xc3, 0xe0},
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
    7, 6, 6, 6, 7, 6, 7, 6, 6, 7, 6, 6, 7, 7, 6, 6,
    6, 7, 6, 7, 6, 7, 6, 6, 6, 7, 6, 6, 6, 7, 6, 6,
    6, 6, 7, 6, 6, 6, 7, 7, 6, 6, 6, 6, 7, 7, 6, 6,
    6, 6, 7, 6, 6, 6, 7, 6, 6, 6, 6, 7, 6, 6, 6, 7,
    6, 6, 6, 7, 7, 6, 6, 7, 6, 6, 6, 6, 6, 6, 6, 7,
    6, 6, 6};
